sattouseiji/SatoOne/docs/cad/README.md

# CAD

Guardar desenhos, versões, tolerâncias, envelopes de componentes e instruções de exportação. Cada alteração mecânica deve referenciar BOM e teste de encaixe.

Consultar `V1_ENCLOSURE_PLAN.md` para a case comercial menor, bateria atrás do teclado e estratégia térmica definida em 2026-09-15. Preservar os STLs V0 definitivos.
