sattouseiji/SatoOne/docs/api/README.md

# API

Documentar contratos de serviços, drivers, eventos e repositórios antes de integrar módulos. Incluir entradas, saídas, erros, estados offline e exemplos de uso.
