sattouseiji/SatoOne/knowledge/display/README.md

# Display

## Estado confirmado — 2026-08-15

- Fabricante/modelo: Waveshare 5DP-CAPLCD-H (variante H).
- Especificação do fabricante: 1024×600, capacitivo, HDMI.
- Medição física com paquímetro: 122.76 × 77.28 × 17.38 mm.
- Regra: a medição física governa o envelope da case; consultar o desenho mecânico oficial H e validar pelo menos uma dimensão contra a peça. Não usar desenhos B ou G.
- Os pontos próprios de fixação existem e devem ser incorporados ao CAD sem inventar coordenadas.

Registrar testes do Waveshare 5" e avaliação do futuro IPS 4": resolução, toque, brilho, consumo, compatibilidade e encaixe.
