sattouseiji/SatoOne/knowledge/radxa/README.md

# Radxa

## Medição física — 2026-08-15

PCB: 65.00 × 30.00 mm; altura máxima com GPIO/pinos/soldas: 11.67 mm; quatro furos Ø2.00 mm, centros 57.37 × 22.00 mm. Os GPIO permanecem instalados e exigem clearance no gabinete. Estes são dados medidos, não especificações de fabricante.

Registrar imagem do SO, HDMI, touchscreen, Wi-Fi, Bluetooth, GPIO, temperatura e limitações confirmadas do Zero 3W.
