sattouseiji/SatoOne/skills/satoone-development/references/08_roadmap.md

# Roadmap

## V0 [PHYSICALLY VALIDATED]

Radxa Zero 3W, Waveshare 5", BBQ20KBD, hub, 2×18650, LX-2BUPS/equivalente, distribuição 5 V, gabinete PLA e Debian funcionais.

## Power V1 Hardware Arrival — até 2026-09-19

1. Receber Li-Po 10 Ah.
2. Receber IP5310.
3. Receber INA219.
4. Fotografar e medir os componentes reais.
5. Confirmar PCM/BMS, conector e polaridade da bateria.
6. Identificar pinout do IP5310.
7. Testar IP5310 sem carga.
8. Confirmar aproximadamente 5 V.
9. Testar somente a Radxa.
10. Testar Radxa + hub.
11. Testar o sistema completo.
12. Medir tensão sob YouTube/carga.
13. Verificar temperatura.
14. Testar carga e uso simultâneos.
15. Decidir posição e integrar INA219.
16. Criar leitura Linux.
17. Implementar indicador de bateria.
18. Implementar low-battery warning.
19. Implementar shutdown automático.
20. Medir autonomia com Li-Po 10 Ah.
21. Redesenhar o Back compacto.
22. Criar a V1 mecânica final.

## Futuro

Cooling ativo somente se testes exigirem. Display 4", microfone, IMU, GPS, NFC, RGB, dock e demais expansões permanecem [FUTURE/IDEA].
