sattouseiji/SatoOne/skills/satoone-development/references/18_future_features.md

# Recursos futuros

Consultar `Future.md` como fonte primária. Battery dashboard e shutdown seguro são próximos itens da V1 após validar o INA219. OTA, voz, biometria, câmera, GPS, LoRa, dock, LTE, NFC, OLED e câmera térmica permanecem futuros; ventoinha é condicional aos testes.
