sattouseiji/SatoOne/skills/satoone-development/references/25_glossary.md

# Glossário

- **BOM:** Bill of Materials, inventário rastreável de componentes.
- **ADR:** registro de uma decisão e suas alternativas.
- **Offline-first:** funções essenciais operam sem rede.
- **HID:** Human Interface Device, por exemplo teclado ou touch USB.
- **Repository Pattern:** abstração de persistência fora da lógica de domínio.
- **V0:** protótipo físico funcional e documentado; não equivale a produto de produção.
- **V1 comercial:** próxima revisão planejada, ainda sujeita a compra, integração e testes.
- **Power-path:** arquitetura que gerencia simultaneamente fonte externa, carga da bateria e alimentação do sistema.
- **Fuel gauge:** circuito que estima estado de carga da bateria a partir de medições/modelo.
- **[PURCHASED] [IN TRANSIT]:** compra confirmada, ainda sem inspeção física; não implica compatibilidade.
- **[CURRENT DESIGN]:** arquitetura escolhida para o próximo teste, ainda sujeita a validação.
- **SUPERSEDED:** informação preservada como histórico, mas não vigente.
