sattouseiji/SatoOne/skills/satoone-development/references/26_commercial_product.md

# Produto comercial e comunicação pública

O SatoOne é proprietário. O repositório e o GitHub Pages formam uma vitrine de desenvolvimento para potenciais compradores, parceiros e financiadores; não são um convite aberto à contribuição nem uma entrega de todos os ativos internos.

## Publicar

- marcos verificáveis, fotos e vídeos do protótipo;
- resultados consolidados e limitações honestas;
- direção do produto, próximos passos e metas claramente rotuladas;
- meios profissionais de manifestar interesse.

## Manter privado ou sanitizar

- credenciais, IP, SSID, MAC, portas e postura detalhada de SSH/firewall;
- logs brutos, dados pessoais e vulnerabilidades exploráveis;
- CAD, software ou processos proprietários não aprovados para divulgação;
- alegações de autonomia, temperatura, compra ou validação sem evidência.

## Cronologia atual

- 2026-09-15: V0 definitiva documentada; direção técnica V1 definida para bateria, telemetria, case e cooling.
- 2026-09-16: estratégia comercial, página pública e documentação consolidada.
