sattouseiji/SatoOne/specifications/ai/README.md

# AI

IA deve ser opcional, configurável e degradável para o Radxa Zero 3W (4 GB RAM). Priorizar execução local; OpenAI, Ollama, LM Studio, Whisper e voz são integrações futuras, não requisitos confirmados da V1.
