sattouseiji/SatoOne/specifications/network/README.md

# Network

O produto é offline-first. Wi-Fi e Bluetooth devem falhar de modo previsível e visível. LTE e LoRa são recursos futuros sujeitos a seleção de módulo, antena, testes e regulamentação.
