sattouseiji/SatoOne/specifications/security/README.md

# Security

Aplicar menor privilégio, atualizações controladas, segredos fora do repositório e validação de dependências. OTA requer assinatura e rollback antes de ser habilitado.
