sattouseiji/SatoOne/specifications/software/README.md

# Software

Stack definido: Debian Bullseye com XFCE, Python 3.9+ e PySide6. Arquitetura: MVC, serviços e adaptadores de hardware separados da interface.
