sattouseiji/SatoOne/specifications/ui/README.md

# UI

Tema escuro: fundo `#050505`, primária `#00BFFF`, destaque `#55CFFF`. Interface PySide6 com componentes próprios, toque e teclado físico; animações devem ser intencionais e compatíveis com o orçamento de desempenho.
