sattouseiji/SatoOne/docs/development/README.md

# Desenvolvimento

Desenvolver com Python/PySide6, MVC, type hints e testes proporcionais ao risco. Consultar `Constraints.md` e `ENGINEERING_BIBLE.md` antes de alterar a arquitetura.

O desenvolvimento serve a um produto proprietário. Consultar `V1_DEVELOPMENT_PLAN.md` para o escopo atual e `V1_ACCEPTANCE_PLAN.md` antes de declarar a V1 validada.
