sattouseiji/SatoOne/docs/deployment/README.md

# Deployment

Documentar imagem Debian, ambiente virtual Python, dependências Qt, autostart, serviços systemd de usuário, rollback e verificação pós-instalação.
