sattouseiji/SatoOne/knowledge/linux/README.md

# Linux

Registrar Debian, virtualenv, dependências, autostart, systemd de usuário, SSH e diagnósticos. Use comandos reais e redija dados sensíveis antes de salvar logs.
