sattouseiji/SatoOne/knowledge/network/README.md

# Network

Registrar Wi-Fi, Bluetooth, conectividade offline, diagnósticos e comportamento de recuperação.
