sattouseiji/SatoOne/knowledge/qt/README.md

# Qt / PySide6

Registrar splash, animações, QPainter, repaint, plugins Qt e dependências gráficas. Documentar FPS, uso de CPU/RAM e versão exata ao concluir testes.
