sattouseiji/SatoOne/skills/satoone-development/references/00_project.md

# SatoOne — DNA do projeto

SatoOne é um computador portátil premium de IA, embarcado e proprietário. A missão é transformar o protótipo funcional em um produto comercial desejável, reparável e evolutivo.

## Princípios

- Construir como uma startup de hardware construindo um produto comercial, nunca como uma demonstração de Raspberry Pi.
- Ser modular, reparável, atualizável, Linux-first, offline-first e adequado a sistemas embarcados.
- Priorizar UX premium, desempenho, arquitetura limpa e manutenção.
- Fazer cada implementação melhorar o produto final; redesenhar quando não for escalável, modular, sustentável ou comercial.
- Manter o desenvolvimento público útil a compradores, parceiros e financiadores, sem expor segredos, rede, segurança operacional ou material interno desnecessário.
- Separar sempre fatos validados, metas, estimativas e componentes candidatos.
