sattouseiji/SatoOne/skills/satoone-development/references/17_security.md

# Segurança

Aplicar menor privilégio, segredos fora do repositório, dependências verificadas e atualizações com rollback. OTA só pode ser entregue com assinatura, verificação e plano de reversão.

Em material público, remover IP/SSID/MAC, portas, postura SSH, usuários, comandos privilegiados, tokens e detalhes que ampliem a superfície de ataque. O relatório interno pode conter dados necessários ao diagnóstico e deve permanecer fora da publicação.
