sattouseiji/SatoOne/skills/satoone-development/references/10_coding_standards.md

# Padrões de código

Usar PEP 8, type hints, docstrings, nomes descritivos, constantes nomeadas e métodos pequenos. Aplicar SOLID, DRY e KISS; preferir composição e evitar classes Deus. Limites: classes até 400 linhas e métodos até 40 linhas.

Não inserir lógica de negócio em UI. Usar serviços, modelos, drivers e workers apropriados. Entregar arquivos completos, com imports e implementação funcional, sem placeholders ou métodos parciais. Propor arquitetura melhor antes de codificar quando houver ganho relevante.
