sattouseiji/SatoOne/skills/satoone-development/references/13_solutions.md

# Soluções validadas

## Propósito

Registrar correções reproduzíveis. Não promover hipótese a solução.

## Template

### SOL-### — Título

- Status: Validada / Revertida / Em validação
- Problema relacionado:
- Ambiente e versões:
- Solução aplicada:
- Por que funcionou:
- Por que tentativas anteriores falharam:
- Evidência e como reproduzir:
- Rollback:
- Melhorias futuras:
