sattouseiji/SatoOne/specifications/manufacturing/README.md

# Manufacturing

## Atualização — 2026-08-15

A Bambu Lab A1 Mini foi recebida e integra oficialmente o laboratório. O desenvolvimento será iterativo, começando por PLA e considerando o volume da impressora em todo CAD. Prioridades: poucos suportes, orientação correta, resistência entre camadas, peças substituíveis, tolerâncias verificadas e baixo consumo de filamento.

Não liberar impressão completa antes de calibration coupons/fit tests aprovados. PETG, TPU e ASA permanecem materiais futuros; ASA não está validado para a configuração atual.

V1: prototipagem com Bambu Lab A1 Mini e PLA. A impressora e filamentos branco, preto e cinza foram comprados, com entrega prevista para 2026-08-05. Confirmar recebimento, tipo exato dos filamentos e estado dos carretéis antes do primeiro uso. Registrar versão do CAD, material, perfil de impressão, orientação, pós-processamento, falhas e resultados para cada peça.
