sattouseiji/SatoOne/docs/manual/README.md

# Manual

Destinado ao usuário e montagem: inicialização, carregamento, manutenção, segurança e resolução de problemas, sempre baseados em comportamento validado.
